dakota127/iSwitchPi/Sources/tiny44/square.h

/* -----------------------------------------------------------------------
 * Title: Analog input changes Frequence of square wave - with PWM
 * Hardware: ATtiny44
 * Diese Version 7 Hz bis ca 160 Hz
 * -----------------------------------------------------------------------*/

#ifndef _SQUARE_H
#define _SQUARE_H

/* Fast PWM */
void pwm_init(void);
void pwm_adc(void);
void pwm_stop(void);
void pwm_start(void);
void pwm_check(void);


#endif  // ifndef _SQUARE_H_
